grafana/TamaGROTchi/src/sprites/grot_0_8x.png

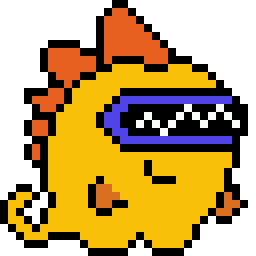
src/sprites/grot_0_8x.png
