grafana/TamaGROTchi/include/lvgl_mem.h

/**
 * @file lvgl_mem.h
 * LVGL v9 LV_STDLIB_CUSTOM implementation backed by PSRAM.
 *
 * LVGL calls these as external C symbols when LV_USE_STDLIB_MALLOC == LV_STDLIB_CUSTOM.
 * Implementation: src/display/lvgl_mem.cpp
 */
#pragma once
/* No includes needed here — declarations are forward-declared in LVGL's lv_mem.c */
